wro2026/WRO1/Electronics/Pictures/Pixabc.com_Compressed_to_500kb_IMG_7014.jpg

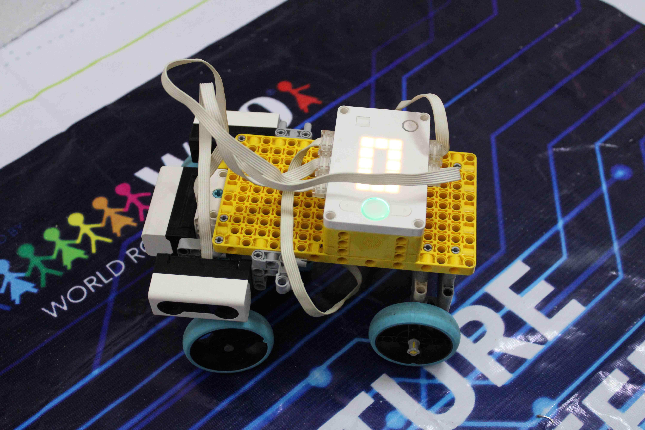
Electronics/Pictures/Pixabc.com_Compressed_to_500kb_IMG_7014.jpg
