wro2026/WRO1/Mechanical Design/Pictures/Pixabc.com_Compressed_to_500kb_IMG_7022.jpg

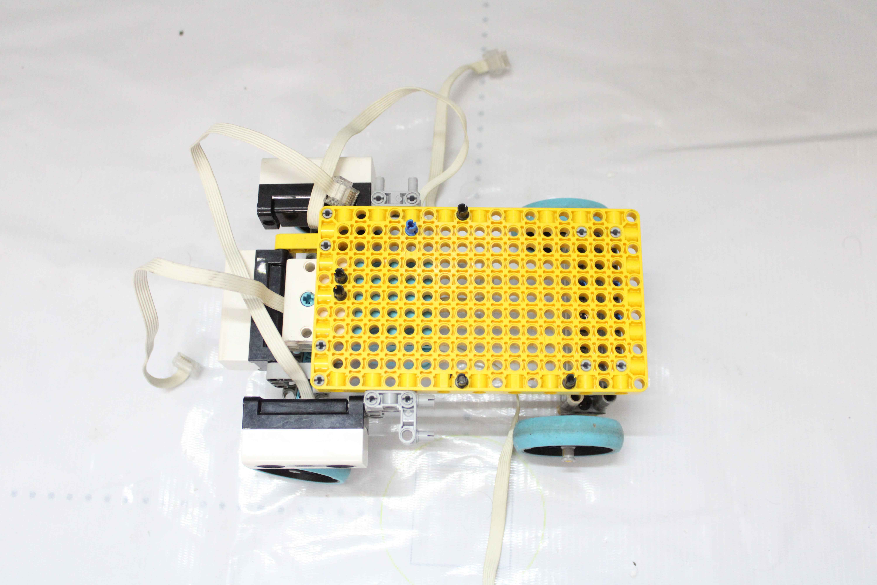
Mechanical Design/Pictures/Pixabc.com_Compressed_to_500kb_IMG_7022.jpg
